impatrq/protcad/Circuitos/Serigrafia.kicad_sch

## KiCad design Circuitos/Serigrafia.kicad_sch (2024-11-07, last stored version)

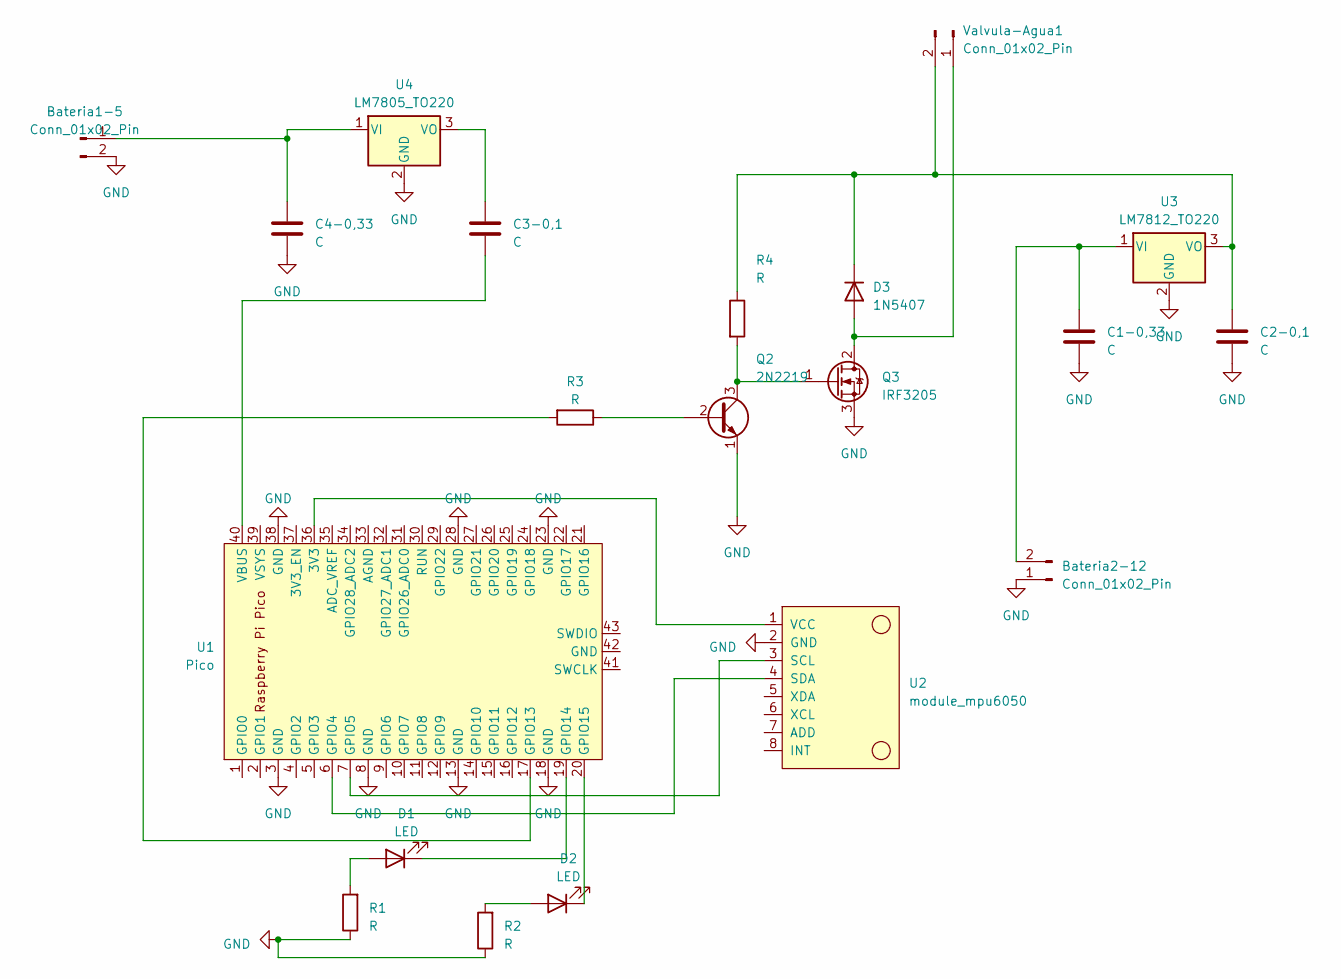
[picture p67: schematic Serigrafia.kicad_sch]

Parts:
Bateria1-5, Bateria2-12: Conn_01x02_Pin; TerminalBlock_bornier-2_P5.08mm
C1-0,33, C2-0,1, C3-0,1, C4-0,33: C; CP_Radial_D4.0mm_P2.00mm
D1, D2: LED; LED_D3.0mm_Clear
D3: 1N5407; D_DO-41_SOD81_P10.16mm_Horizontal
Q2: 2N2219; TO-39-3
Q3: IRF3205; TO-220-3_Vertical
R1, R2, R3, R4: R; R_Axial_DIN0207_L6.3mm_D2.5mm_P10.16mm_Horizontal
U1: Pico; RPi_Pico_SMD_TH
U2: module_mpu6050
U3: LM7812_TO220; TO-220-3_Vertical
U4: LM7805_TO220; TO-220-3_Vertical
Valvula-Agua1: Conn_01x02_Pin; TerminalBlock_bornier-2_P5.08mm

Connections:
GND: Bateria1-5.2, Bateria2-12.1, C1-0,33.2, C2-0,1.2, C4-0,33.2, Q2.1 (E), Q3.3 (S), R1.1, R2.1, U1.3 (GND), U1.8 (GND), U1.13 (GND), U1.18 (GND), U1.23 (GND), U1.28 (GND), U1.38 (GND), U2.2 (GND), U3.2 (GND), U4.2 (GND)
unnamed: Bateria1-5.1, C4-0,33.1, U4.1 (VI)
unnamed: Bateria2-12.2, C1-0,33.1, U3.1 (VI)
unnamed: C2-0,1.1, D3.1 (K), R4.1, U3.3 (VO), Valvula-Agua1.2
unnamed: C3-0,1.1, U4.3 (VO)
unnamed: C3-0,1.2, U1.40 (VBUS)
unnamed: D1.1 (K), U1.19 (GPIO14)
unnamed: D1.2 (A), R1.2
unnamed: D2.1 (K), U1.20 (GPIO15)
unnamed: D2.2 (A), R2.2
unnamed: D3.2 (A), Q3.2 (D), Valvula-Agua1.1
unnamed: Q2.2 (B), R3.1
unnamed: Q2.3 (C), Q3.1 (G), R4.2
unnamed: R3.2, U1.17 (GPIO13)
unnamed: U1.6 (GPIO4), U2.4 (SDA)
unnamed: U1.7 (GPIO5), U2.3 (SCL)
unnamed: U1.36 (3V3), U2.1 (VCC)
